metznick/S3XY-Dash_Mount/pictures/20260915_163913.jpg

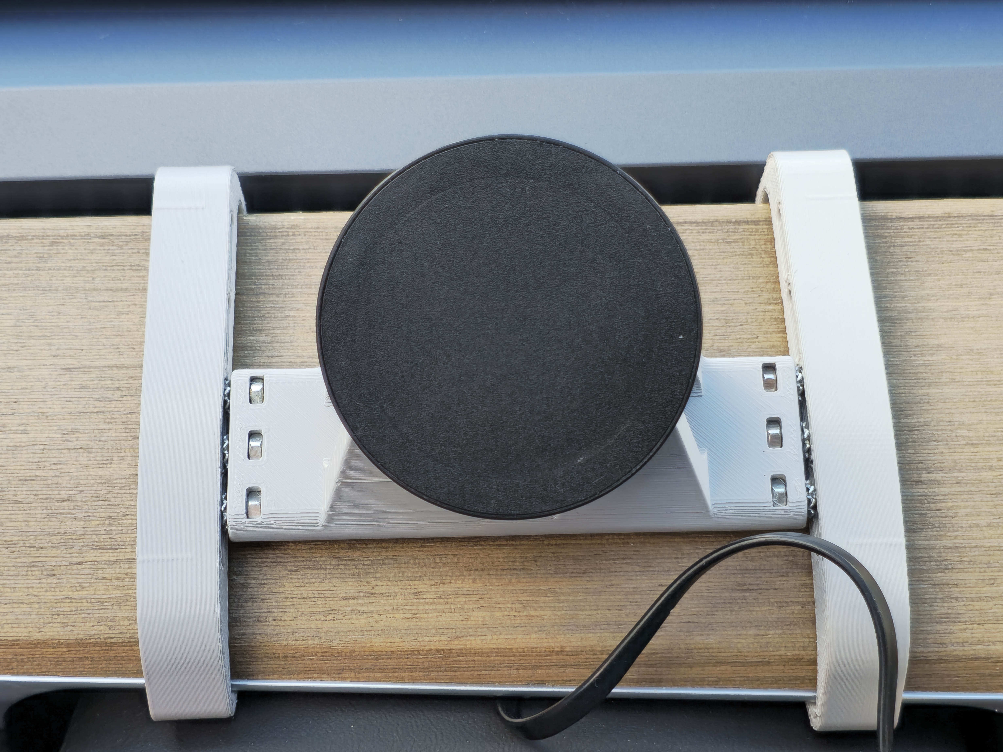
pictures/20260915_163913.jpg
