metznick/S3XY-Dash_Mount/pictures/20260813_235348.jpg

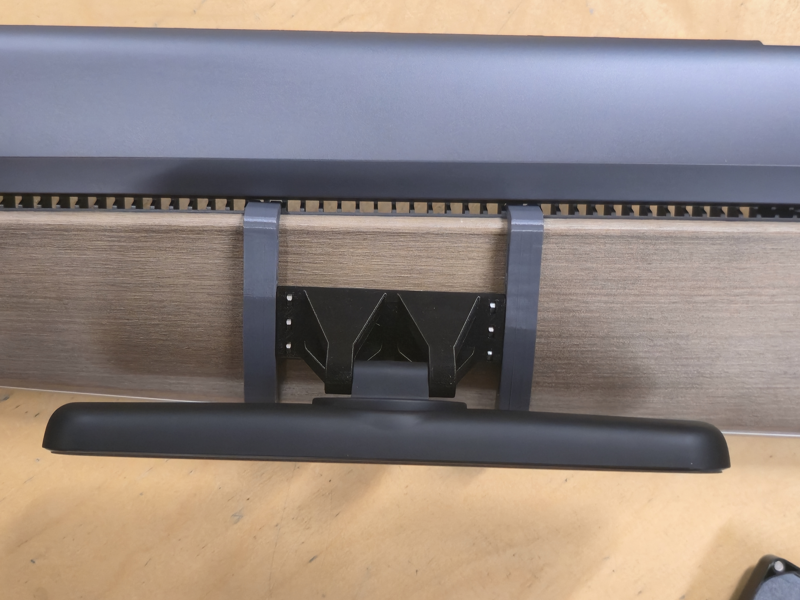
pictures/20260813_235348.jpg
